Neurotech-Hub/FED4/src/FED4.h

#ifndef FED4_h
#define FED4_h


// note there is a known issue with FastLED 3.10.3 on ESP32-S3 devices
// keep FastLED version 3.10.2 until this issue is fixed in the main FastLED repository
// https://github.com/FastLED/FastLED/issues/5100

#include <Arduino.h>
#include <map>
#include <string>
#include <Adafruit_MCP23X17.h>  // version 2.3.2 
#include "Adafruit_MAX1704X.h"  // version 1.0.3
#include <Stepper.h>  // version 1.1.3
#include <Adafruit_NeoPixel.h> // version 1.15.2
#include <FastLED.h> // version 3.10.2 
#include <Wire.h> 
#include <Adafruit_GFX.h>  // version 1.12.3
#include <Fonts/FreeSans9pt7b.h>
#include <Fonts/Org_01.h>
#include <esp_adc_cal.h>
#include "esp_sleep.h"
#include "RTClib.h" //Adafruit version, 2.1.4
#include <SD.h> //ESP32 version
#include "FS.h"
#include <Adafruit_BME680.h> //version 2.0.5
#include <SPI.h>
#include <driver/adc.h>
#include <ESP_I2S.h>  // New I2S API for ESP32 core 3.x
#include <driver/rtc_io.h>
#include <driver/touch_pad.h>
#include <Preferences.h>
#include <ArduinoJson.h>
#include <Adafruit_LIS3DH.h> //version 1.3.0
#include <Adafruit_Sensor.h>
#include "Adafruit_MLX90393.h" //version 2.0.5
#include "SparkFun_VL53L1X.h" //version 1.2.12
#include "Adafruit_STHS34PF80.h"  //version 1.0.2
#include "Adafruit_VEML7700.h" //version 2.1.6
#include <ESP32Time.h> //version 2.0.6

// Optional Hublink integration - can be excluded via compiler directive
#ifndef FED4_EXCLUDE_HUBLINK
#include <Hublink.h>
#endif

// Pin Definitions
#include "FED4_Pins.h"

// Board Version: set to 162 for v1.6.2 or 163 for v1.6.3
#ifndef FED4_BOARD_VERSION
  #define FED4_BOARD_VERSION 163
#endif

#if FED4_BOARD_VERSION == 163
  #define FED4_BOARD_VERSION_STR "1.6.3"
#elif FED4_BOARD_VERSION == 162
  #define FED4_BOARD_VERSION_STR "1.6.2"
#else
  #error "Unsupported FED4_BOARD_VERSION. Use 162 (v1.6.2) or 163 (v1.6.3)."
#endif

// Device Constants
static const uint8_t LIS3DH_I2C_ADDRESS = 0x19;   // Default I2C address for LIS3DH accelerometer
#if FED4_BOARD_VERSION == 163
  static const uint8_t MLX90393_I2C_ADDRESS = 0x10; // MLX90393 I2C address for board v1.6.3
#else
  static const uint8_t MLX90393_I2C_ADDRESS = 0x0C; // MLX90393 I2C address for board v1.6.2
#endif

// Display Colors and Constants
static const uint8_t DISPLAY_BLACK = 0;
static const uint8_t DISPLAY_WHITE = 1;
static const uint8_t DISPLAY_INVERSE = 2;
static const uint8_t DISPLAY_NORMAL = 3;

// Common display dimensions
static const uint16_t DISPLAY_WIDTH = 144;
static const uint16_t DISPLAY_HEIGHT = 168;

static const uint8_t NUM_STRIP_LEDS = 8;
static const uint8_t NUMPIXELS = 1;
static const uint16_t MOTOR_STEPS = 512;
static const uint8_t MOTOR_SPEED = 24;

static const float TOUCH_THRESHOLD = 0.2; // percentage of baseline change to trigger poke - note that when plugged in by USB this can be much more sensitive than on battery power, due to different grounding
static const char *META_FILE = "/meta.json";

static const char *PREFS_NAMESPACE = "fed4";
static const bool PREFS_RO_MODE = true;
static const bool PREFS_RW_MODE = false;

// current very public-oriented, consider pushing some to private
class FED4 : public Adafruit_GFX
{
public:
    // Constructor declaration only
    FED4();
    static const char libraryVer[];

    // Initialization
    bool begin(const char *programName = nullptr);

    // Hublink integration
    bool useHublink = false; // Default to false, can be set by user
    bool initializeHublink();
    void syncHublink();
    static void onHublinkTimestampReceived(uint32_t timestamp);

    // Motion sensor (STHS34PF80) control
    bool useMotionSensor = true; // Default to true, can be set to false to disable STHS34PF80

    // Button functions
    bool initializeButtons();
    static void IRAM_ATTR onButton1WakeUp();
    static void IRAM_ATTR onButton2WakeUp();
    static void IRAM_ATTR onButton3WakeUp();
    void checkButton1();
    void checkButton2();
    void checkButton3();

    // Corefunctions
    void feed();
    void run();
    
    // Game functions
    void pong();

    // Sleep configuration
    int sleepSeconds = 4; // how many seconds to sleep between timer based wake-ups
    bool sleepyLEDs = true; // Flag to control whether LEDs stay on during sleep (true = LEDs sleep with sleep, false = LEDs stay on during sleep)

    // Menu functions
    void menu();
    void menuStart();
    void menuProgram();
    void menuMouseId();
    void menuSex();
    void menuStrain();
    void menuAge();
    void menuAudio();
    void menuRTC();
    void menuEnd();

    // Sensor polling
    void pollSensors(int minToUpdateSensors = 10);
    void startupPollSensors();

    // Pellet functions
    bool checkForPellet();
    bool didPelletDrop();
    bool pelletPresent;
    bool pelletDropped;
    void initFeeding();
    void handlePelletSettling();
    void handlePelletInWell();
    void finishFeeding();
    void dispense();
    unsigned long pelletDropTime;
    unsigned long pelletWellTime;
    bool dispenseError = false;
    void handleJams();

    // TRRS input/output connector functions
    bool initializeTRRS();
    void outputPulse(uint8_t trss, uint8_t duration);

    // Clock variables
    int currentHour;
    int currentMinute;
    int currentSecond;
    unsigned long unixtime;

    // Stepper motor functionality (defined in FED4_Motor.cpp)
    bool initializeMotor();
    void releaseMotor();
    void minorJamClear();
    void majorJamClear();
    void vibrateJamClear();
    void jammed();

    // Timeout functionality (defined in FED4_Timeout.cpp)
    void timeout(uint16_t min, uint16_t max);

    // Haptic motor vibration stimuli
    void hapticBuzz(uint8_t duration = 100);
    void hapticDoubleBuzz(uint8_t duration = 25);
    void hapticTripleBuzz(uint8_t duration = 5);
    void hapticRumble(uint16_t duration_ms = 300);

    // Touch sensor management (defined in FED4_Touch.cpp)
    bool initializeTouch();
    void calibrateTouchSensors(bool checkStability = false);
    void interpretTouch();
    static void IRAM_ATTR onTouchWakeUp();
    void resetTouchFlags(); // Reset all touch flags to false
    void logTouchEvent(); // Log touch events separately from critical path
    static uint8_t wakePad; // 0=none, 1=left, 2=center, 3=right

    // Pixel an Strip control (defined in FED4_LEDs.cpp)
    // (strip)
    bool initializeStrip();
    void setStripBrightness(uint8_t brightness);
    void colorWipe(const char *colorName, unsigned long wait);
    void colorWipe(uint32_t color, unsigned long wait);
    void stripTheaterChase(const char *colorName, unsigned long wait, unsigned int groupSize = 3, unsigned int numChases = 10);
    void stripTheaterChase(uint32_t color, unsigned long wait, unsigned int groupSize = 3, unsigned int numChases = 10);
    void stripRainbow(unsigned long wait, unsigned int numLoops);
    void randomMotion(float motionStrength, uint32_t color, unsigned long frameDelay = 75, unsigned long durationMs = 3000);
    void randomMotion(float motionStrength, const char *colorName = "blue", unsigned long frameDelay = 75, unsigned long durationMs = 3000);
    void lightsOff();
    void setStripPixel(uint8_t pixel, uint32_t color);
    void leftLight(uint32_t color);
    void leftLight(uint32_t color, uint8_t brightness);
    void centerLight(uint32_t color);
    void centerLight(uint32_t color, uint8_t brightness);
    void rightLight(uint32_t color);
    void rightLight(uint32_t color, uint8_t brightness);
    void setStripPixel(uint8_t pixel, const char *colorName);
    void leftLight(const char *colorName);
    void leftLight(const char *colorName, uint8_t brightness);
    void centerLight(const char *colorName);
    void centerLight(const char *colorName, uint8_t brightness);
    void rightLight(const char *colorName);
    void rightLight(const char *colorName, uint8_t brightness);
    // (pixel)
    bool initializePixel();
    void setPixBrightness(uint8_t brightness);
    void setPixColor(uint8_t r, uint8_t g, uint8_t b, uint8_t brightness = 5);
    void setPixColor(const char *colorName, uint8_t brightness = 5);
    void bluePix(uint8_t brightness = 5);
    void greenPix(uint8_t brightness = 5);
    void redPix(uint8_t brightness = 5);
    void purplePix(uint8_t brightness = 5);
    void yellowPix(uint8_t brightness = 5);
    void cyanPix(uint8_t brightness = 5);
    void whitePix(uint8_t brightness = 5);
    void orangePix(uint8_t brightness = 5);
    void noPix();
    // (shared)
    uint32_t getColorFromString(const char *colorName);

    // Display functions (defined in FED4_Display.cpp)
    bool initializeDisplay();
    void updateDisplay();
    void displayTask();
    void displayMouseId();
    void displayStrain();
    void displaySex();
    void displayAge();
    void displayAudio();
    void displayCounters();
    void displayDateTime();
    void displayEnvironmental();
    void displayBattery();
    void displaySDCardStatus();
    void displayIndicators();
    void startupAnimation();
    void displayInitStatus(const char* message);
    void displayLowBatteryWarning();
    void displayActivityMonitor();
    void displayActivityCounters();

    void serialStatusReport();

    // Sleep management (defined in FED4_Sleep.cpp)
    void sleep(int seconds);
    void sleep();
    void startSleep();
    void wakeUp();
    void handleTouch();
    unsigned long pollSensorsTimer = 0;

    
    bool initializeLDOs();
    void LDO2_ON();
    void LDO2_OFF();
    void LDO3_ON();
    void LDO3_OFF();

    // SD card functions (defined in FED4_SD.cpp)
    bool initializeSD();
    bool createMetaJson();
    bool createLogFile();
    bool logData(const String &newEvent = "");
    String getMetaValue(const char *rootKey, const char *subKey);
    bool setMetaValue(const char *rootKey, const char *subKey, const char *value);
    void setProgram(String program);
    void setMouseId(String mouseId);
    void setSex(String sex);
    void setStrain(String strain);
    void setAge(String age);
    void handleSDCardError();
    bool isSDCardAvailable() const { return sdCardAvailable; }
    
    // Sequence display methods
    void setSequenceDisplay(const String& sequence, int index, int level);

    // Public counters and timing
    int pelletCount;
    int centerCount;
    int leftCount;
    int rightCount;
    int blockPokeCount;
    int blockPelletCount;
    int FR;
    String currentSequence;  // For display purposes
    int currentSequenceIndex; // Current position in sequence
    int currentSequenceLevel; // Current level (FR)
    int wakeCount = 0;
    bool leftTouch;
    bool centerTouch;
    bool rightTouch;
    bool motionDetected = false;  // Track motion detection status
    int motionCount = 0;          // Aggregate motion detections between 5-minute intervals
    float motionPercentage = 0.0; // Percentage of motion detections in the last 5-minute period
    int pollCount = 0;            // Track total number of polls in each 5-minute period
    unsigned long waketime;
    bool lastMotionPositive = false; // Debounce: require two consecutive positives

    // RTC functions
    bool initializeRTC();
    void updateRTC();
    DateTime now();
    void adjustRTC(uint32_t timestamp);
    void updateTime();
    bool forceRTCUpdate = false; // Set to true to force RTC update on next initialization

    // Vitals functions (defined in FED4_Vitals.cpp)
    float getBatteryVoltage();
    float getBatteryPercentage();
    float getTemperature();
    float getHumidity();
    float getPressure();
    float getGasResistance();
    bool getTempAndHumidity(float &temp, float &hum); // Efficient combined read
    bool getAllBME680Data(float &temp, float &hum, float &pres, float &gas); // Get all BME680 values
    float getLux();
    float getWhite();
    bool initializeLightSensor();
    bool reinitializeLightSensor();
    

    // variables to store temp/humidity/pressure/gas and battery info so we don't have to keep pinging the chips every time
    float temperature = -1.0;
    float humidity = -1.0;
    float pressure = -1.0;
    float gasResistance = -1.0;
    float lux = -1.0;
    float white = -1.0;
    float cellVoltage = 0.0;
    float cellPercent = 0.0;
    unsigned long lastPollTime = 0; // make this a large negative so FED polls sensors at first startup

    // Speaker functions (defined in FED4_Speaker.cpp)
    bool initializeSpeaker();
    struct Tone
    {
        uint32_t frequency;
        uint32_t duration_ms;
        float amplitude = 0.25;
    };
    void playTone(uint32_t frequency = 500, uint32_t duration_ms = 200, float amplitude = 0.25);
    void playTones(const Tone *tones, size_t count);
    void enableAmp(bool enable);
    void silence();
    void unsilence();
    void resetSpeaker();

    // Sound stimuli
    void playStartup();
    void bopBeep();
    void resetJingle();
    void menuJingle();
    void lowBeep();
    void highBeep();
    void higherBeep();
    void click();
    void soundSweep(uint32_t startFreq = 500, uint32_t endFreq = 1500, uint32_t duration_ms = 1000);
    void noise(uint32_t duration_ms = 500, float amplitude = 1);

    // "Super Mario"-style sound effects (tone synthesis)
    void marioCoin();
    void marioJump();
    void marioPipe();
    void marioFireball();
    void marioMushroom();

    void setEvent(const String &newEvent)
    {
        event = newEvent;
    }

    String getEvent() const
    {
        return event;
    }

    bool pelletReady;
    bool feedReady;
    int photogate1State;
    String event = "";
    float retrievalTime;
    float pokeDuration = 0.0;
    int touchPadLeftBaseline;
    int touchPadCenterBaseline;
    int touchPadRightBaseline;
    int motorTurns;
    int reBaselineTouches;
    char filename[32];
    bool sdCardAvailable = true; // Track if SD card operations are available
    bool audioSilenced = false; // Track if audio has been silenced

    void clearDisplay();
    void refresh();
    void drawPixel(int16_t x, int16_t y, uint16_t color);



    // Accelerometer functions (defined in FED4_Accel.cpp)
    bool initializeAccel();
    void setAccelRange(lis3dh_range_t range);
    void setAccelPerformanceMode(lis3dh_mode_t mode);
    void setAccelDataRate(lis3dh_dataRate_t dataRate);
    bool getAccelEvent(sensors_event_t *event);
    void readAccel(float &x, float &y, float &z);
    bool accelDataReady();

    // Magnet functions (defined in FED4_Magnet.cpp)
    bool initializeMagnet();
    void setMagnetGain(mlx90393_gain_t gain);
    mlx90393_gain_t getMagnetGain();
    bool readMagnetData(float &x, float &y, float &z);
    bool getMagnetEvent(sensors_event_t *event);
    void configureMagnet(mlx90393_gain_t gain = MLX90393_GAIN_5X);

    // ToF sensor functions (defined in FED4_ToF.cpp)
    bool initializeToF();
    int prox();

    // Motion sensor functions (defined in FED4_Motion.cpp)
    bool initializeMotion();
    bool motion();
    void resetMotionCounters();

    // Drop sensor functions
    bool initializeDropSensor();

    // Memory monitoring function
    void printMemoryStatus();

    ~FED4()
    {
        if (displayBuffer)
        {
            free(displayBuffer);
            displayBuffer = nullptr;
        }
        preferences.end(); // Ensure preferences is closed
    }

private:
    // Hardware objects
    Adafruit_MCP23X17 mcp;
    Adafruit_MAX17048 maxlipo;
    RTC_DS3231 rtc;
    ESP32Time Inrtc;
    Adafruit_BME680 bme;
    Adafruit_NeoPixel pixels;
    Stepper stepper;
    TwoWire I2C_2;
    CRGB strip_leds[NUM_STRIP_LEDS];
    Adafruit_LIS3DH accel;
    Adafruit_MLX90393 magnet;
    Adafruit_STHS34PF80 motionSensor;
    Adafruit_VEML7700 lightSensor;
    I2SClass i2s;  // New I2S driver object for ESP32 core 3.x

// Hublink integration
#ifndef FED4_EXCLUDE_HUBLINK
    Hublink hublink;
#endif
    // Device state variables
    esp_adc_cal_characteristics_t *adc_cal;
    uint32_t millivolts;
    String program;
    String mouseId;
    String sex;
    String strain;
    String age;
    bool dropSensorAvailable; // Flag to store drop sensor availability status
    bool motionSensorInitialized; // Flag to track if motion sensor baseline is established

    // RTC functions
    Preferences preferences;
    String getCompileDateTime();
    bool isNewCompilation();
    void updateCompilationID();

    uint16_t lastTouchValue; // Store the touch value that triggered the interrupt

    uint8_t *displayBuffer = nullptr;
    bool vcom;
    void sendDisplayCommand(uint8_t cmd);

    friend class FED4_Display;
    friend class FED4_LED;
    friend class FED4_Motor;
    friend class FED4_RTC;
    friend class FED4_SD;
    friend class FED4_Touch;
    friend class FED4_Vitals;
    friend class FED4_Feed;
    friend class FED4_Begin;
    friend class FED4_Audio;
    friend class FED4_Magnet;
    friend class FED4_Accel;
    friend class FED4_Menu;
    friend class FED4_Motion;
    friend class FED4_Sleep;
    friend class FED4_Timeout;
    friend class FED4_Prox;
};

// Standard ASCII 5x7 font
static const unsigned char font[] PROGMEM = {
    0x00, 0x00, 0x00, 0x00, 0x00, // space
    0x00, 0x00, 0x5F, 0x00, 0x00, // !
    0x00, 0x07, 0x00, 0x07, 0x00, // "
    // ... rest of font data ...
};

#endif
