Neurotech-Hub/FED4/src/FED4_Feed.cpp

#include "FED4.h"

/**
 * Feeds the mouse by dispensing a pellet from the hopper
 */
void FED4::feed()
{
    initFeeding();
    dispense(); 
    handlePelletSettling();
    handlePelletInWell();
    finishFeeding();
}

void FED4::initFeeding() {
    pelletPresent = checkForPellet();
    pelletDropped = didPelletDrop();
    pelletReady = false;
    dispenseError = false;
    //lightsOff();
    // Serial.println("Feeding!");
}

void FED4::dispense() {
    while (!pelletPresent && !pelletDropped) // while no pellet is present and none has dropped
    {                     
        redPix();
        // check if pellet has dropped or is present
        pelletDropped = didPelletDrop();
        pelletPresent = checkForPellet();
        pelletReady = true;
        
        // Check if button is pressed - if so, fake pelletPresent to exit dispense
        if (digitalRead(BUTTON_1) == 1) {
            hapticDoubleBuzz();
            marioPipe();
            pelletPresent = true;
        }
        
        // Increment block pellet count when pellet drops
        if (pelletDropped) {
            blockPelletCount++;
        }

        // small motor movement
        stepper.step(-10);
        delay(2);
        motorTurns++;
        // delay for 1s roughly each pellet position
        if (motorTurns % 25 == 0)
        {
            Serial.print("Dispensing... ");
            Serial.println(motorTurns/25);
            releaseMotor();
            delay(1000);
        }

        //handle jam movements
        handleJams();
    }
}

void FED4::handleJams() {
        // if stepper is called too many times without a dispense do a small movement to remove jam
        if (motorTurns % 100 == 0)
        {
            minorJamClear();
        }

        if (motorTurns % 200 == 0)
        {
            vibrateJamClear();
        }

        if (motorTurns > 2000)  //how many motorTurns before FED4 stops trying and shuts off?  Each full rotation of the hopper is ~1000 motorTurns
        {
            jammed();
    }
}

void FED4::handlePelletSettling() {
        if (pelletReady) {
        // Serial.println("PelletDrop");
        pelletDropTime = millis();
        pelletCount++;
        logData("PelletDrop");
        }        
  
    releaseMotor();

    // Wait up to 500ms for pellet to settle in well if 500ms passes without detection, set dispenseError to true
    unsigned long startWait = millis();
    bool pelletDetected = false;

    while (millis() - startWait < 500) {
        if (checkForPellet()) {
            pelletDetected = true;
            pelletWellTime = millis();
            break; // Exit if pellet is detected
        }
        delay(10);
    }

    // if pellet is not detected, set dispenseError to true
    if (!pelletDetected) {
        dispenseError = true;
    }

    // Calculate time since pellet drop
    retrievalTime = (millis() - pelletWellTime) / 1000.0;
    // Serial.println("Pellet in Well");
}   

void FED4::handlePelletInWell() {
    pelletPresent = checkForPellet();
    updateDisplay();
    
    // Reset wakePad at start to clear any stale interrupt flags
    wakePad = 0;
    
    while (pelletPresent)
    { // while pellet is in well, monitor for pokes and retrieval time
        bluePix(); 
        pelletPresent = checkForPellet();

        retrievalTime = (static_cast<float>(millis() - pelletWellTime)) / 1000.0f;
        if (retrievalTime > 20)
            break;

        // wakePad mapping (physical pad to touch mapping is rotated):
        // Physical LEFT pad (wakePad=1) → triggers centerTouch
        // Physical CENTER pad (wakePad=2) → triggers rightTouch
        // Physical RIGHT pad (wakePad=3) → triggers leftTouch
        if (wakePad == 3) {  // RIGHT pad interrupt → Left touch
            // Verify touch is actually above threshold (rising edge, not falling edge)
            float rightDev = abs((float)touchRead(TOUCH_PAD_RIGHT) / touchPadRightBaseline - 1.0);
            if (rightDev >= TOUCH_THRESHOLD) {
                unsigned long pokeStartTime = millis();
                leftCount++;
                retrievalTime = 0.0;
                dispenseError = false;
                // Serial.println("LeftWithPellet");
                logData("LeftWithPellet");
                click();
                updateDisplay();
                outputPulse(1, 100);
                // Wait for touch to return to baseline before allowing next detection
                while (abs((float)touchRead(TOUCH_PAD_RIGHT) / touchPadRightBaseline - 1.0) >= TOUCH_THRESHOLD) {
                    delay(10);
                }
                pokeDuration = (float)(millis() - pokeStartTime);
            }
            wakePad = 0; // Reset after handling (whether processed or not)
        }
        else if (wakePad == 2) {  // CENTER pad interrupt → Right touch
            // Verify touch is actually above threshold (rising edge, not falling edge)
            float centerDev = abs((float)touchRead(TOUCH_PAD_CENTER) / touchPadCenterBaseline - 1.0);
            if (centerDev >= TOUCH_THRESHOLD) {
                unsigned long pokeStartTime = millis();
                rightCount++;
                retrievalTime = 0.0;
                dispenseError = false;
                // Serial.println("CenterWithPellet");
                logData("CenterWithPellet"); 
                click();
                updateDisplay();
                bluePix();
                outputPulse(2, 100);
                // Wait for touch to return to baseline before allowing next detection
                while (abs((float)touchRead(TOUCH_PAD_CENTER) / touchPadCenterBaseline - 1.0) >= TOUCH_THRESHOLD) {
                    delay(10);
                }
                pokeDuration = (float)(millis() - pokeStartTime);
            }
            wakePad = 0; // Reset after handling (whether processed or not)
        }
        else if (wakePad == 1) {  // LEFT pad interrupt → Center touch
            // Verify touch is actually above threshold (rising edge, not falling edge)
            float leftDev = abs((float)touchRead(TOUCH_PAD_LEFT) / touchPadLeftBaseline - 1.0);
            if (leftDev >= TOUCH_THRESHOLD) {
                unsigned long pokeStartTime = millis();
                centerCount++;
                retrievalTime = 0.0;
                dispenseError = false;
                // Serial.println("CenterWithPellet");
                logData("CenterWithPellet");
                click();
                updateDisplay();
                bluePix();
                outputPulse(2, 100);
                // Wait for touch to return to baseline before allowing next detection
                while (abs((float)touchRead(TOUCH_PAD_LEFT) / touchPadLeftBaseline - 1.0) >= TOUCH_THRESHOLD) {
                    delay(10);
                }
                pokeDuration = (float)(millis() - pokeStartTime);
            }
            wakePad = 0; // Reset after handling (whether processed or not)
        }
        
        delay(10); // Small delay to prevent excessive CPU usage
    }
}

void FED4::finishFeeding() {
        purplePix();
    // Serial.println("Pellet Removed");

    if (pelletReady) {
        if (dispenseError) {
            retrievalTime = 0.0;
            logData("PelletNotDetected");
        } else {
            logData("PelletTaken");
            blockPokeCount = 0;  // Reset block poke count when pellet is taken
        }
    }

    // Reset variables
    pelletReady = false;
    retrievalTime = 0.0;
    dispenseError = false;
    
    // Reset touch states after handling the feed
    leftTouch = false;
    centerTouch = false;
    rightTouch = false;

    // Rebaseline touch sensors
    reBaselineTouches = 3;
    if ((leftCount + rightCount + centerCount) % reBaselineTouches == 0 && (leftCount + rightCount + centerCount) > 5)
    {
        calibrateTouchSensors();
    }

}

/** 
 * Checks if the pellet is present in the center port
 * 
 * @return bool - true if pellet is present, false otherwise
 */
bool FED4::checkForPellet()
{
    return !mcp.digitalRead(EXP_PHOTOGATE_1);
}

/** 
 * Checks if the pellet is present dropped 
 * 
 * @return bool - true if pellet dropped, false otherwise
 */
bool FED4::didPelletDrop()
{
    if (dropSensorAvailable) {
        //With drop sensor use:
        return !mcp.digitalRead(EXP_PHOTOGATE_4);
    } else {
        //Without drop sensor use:
        return false; // Always return false when sensor is not available
    }
}

/**
 * Initializes the drop sensor and checks its status
 * 
 * @return bool - true if drop sensor is working (HIGH), false if broken or not present (LOW)
 */
bool FED4::initializeDropSensor()
{
    // Read the drop sensor status
    bool sensorStatus = mcp.digitalRead(EXP_PHOTOGATE_4);
    
    // Set the flag based on sensor status
    dropSensorAvailable = sensorStatus;
    
    // Return true if HIGH (sensor is good), false if LOW (broken or not present)
    return sensorStatus;
}
