Neurotech-Hub/FED4/src/FED4_Buttons.cpp

#include "FED4.h"

// Interrupt handler for BUTTON_1
void IRAM_ATTR FED4::onButton1WakeUp() {
}

// Interrupt handler for BUTTON_2
void IRAM_ATTR FED4::onButton2WakeUp() {
}

// Interrupt handler for BUTTON_3
void IRAM_ATTR FED4::onButton3WakeUp() {
}

bool FED4::initializeButtons() {
    // Configure BUTTON_1, BUTTON_2, and BUTTON_3 as inputs with internal pulldown
    gpio_config_t io_conf = {};
    io_conf.intr_type = GPIO_INTR_HIGH_LEVEL;
    io_conf.pin_bit_mask = (1ULL << BUTTON_1) | (1ULL << BUTTON_2) | (1ULL << BUTTON_3);
    io_conf.mode = GPIO_MODE_INPUT;
    io_conf.pull_down_en = GPIO_PULLDOWN_ENABLE;
    io_conf.pull_up_en = GPIO_PULLUP_DISABLE;
    
    esp_err_t err = gpio_config(&io_conf);
    if (err != ESP_OK) {
        Serial.println("Failed to configure GPIO");
        return false;
    }
    
    // Enable wake-up on GPIO for all buttons
    err = gpio_wakeup_enable((gpio_num_t)BUTTON_1, GPIO_INTR_HIGH_LEVEL);
    if (err != ESP_OK) {
        Serial.println("Failed to enable GPIO wakeup for Button 1");
        return false;
    }
    
    err = gpio_wakeup_enable((gpio_num_t)BUTTON_2, GPIO_INTR_HIGH_LEVEL);
    if (err != ESP_OK) {
        Serial.println("Failed to enable GPIO wakeup for Button 2");
        return false;
    }
    
    err = gpio_wakeup_enable((gpio_num_t)BUTTON_3, GPIO_INTR_HIGH_LEVEL);
    if (err != ESP_OK) {
        Serial.println("Failed to enable GPIO wakeup for Button 3");
        return false;
    }
    
    err = esp_sleep_enable_gpio_wakeup();
    if (err != ESP_OK) {
        Serial.println("Failed to enable GPIO wakeup in sleep");
        return false;
    }
    return true;
}

// Checks if feed button is held and dispenses test pellet after 1 second
void FED4::checkButton1() {
  int holdTime = 0;
  while (digitalRead(BUTTON_1) == 1) {
    delay(100);
    holdTime += 100;
    if (holdTime >= 1000) {
        marioMushroom();
        delay (500);
        Serial.println("********** TEST PELLET DISPENSE **********");
        feed();
        break;
    }
  }
}

// Checks if reset button is held and performs device reset after 1 second
void FED4::checkButton2() {
  int holdTime = 0;
  while (digitalRead(BUTTON_2) == 1) {
    delay(100);
    holdTime += 100;
    if (holdTime >= 1000) {
        colorWipe("red", 100); // red
        resetJingle();
        Serial.println("********** BUTTON 2 FORCED RESET! **********");
        esp_restart();
        break;
    }
  }
}

// Checks if Button 3 is held for silence toggle (500ms) or menu (1500ms)
void FED4::checkButton3() {
  int holdTime = 0;
  
  while (digitalRead(BUTTON_3) == 1) {
    delay(100);
    holdTime += 100;
    
    // At 500ms: Provide haptic feedback for audio toggle threshold
    if (holdTime == 500) {
      // temporarily unmute audio even if it is silenced
      digitalWrite(AUDIO_SD, HIGH);
      click();
    }
    
    // At 1500ms: Enter menu with double haptic feedback (no audio toggle)
    if (holdTime >= 1500) {
        hapticDoubleBuzz(100);
        Serial.println("********** BUTTON 3 MENU START **********");
        menu();
        break;
    }
  }
  
  // Only toggle audio if button was released between 500ms and 1500ms
  if (holdTime >= 500 && holdTime < 1500) {
    if (audioSilenced) {
        unsilence();
        Serial.println("********** AUDIO ENABLED **********");
    } else {
        silence();
        Serial.println("********** AUDIO DISABLED **********");
    }
  }
}
