Neurotech-Hub/FED4/src/FED4_Serial.cpp

#include "FED4.h"

void FED4::serialStatusReport()
{
    if (wakeCount == 0) {
        Serial.println("********** Ready to go! **********");
    }
    
    // Check if motion sensor is disabled
    if (!useMotionSensor || isnan(motionPercentage)) {
        Serial.printf("%02d/%02d/%02d %02d:%02d:%02d | %.1fC - %.1f%% - %.1fhPa - %.1fKΩ | %.1fLux | %.2fV(%.1f%%) | No Motion | Pel %d | Left/Cent/Right %d/%d/%d | Poke %.0fms | Mem %d | Wake %d\n",        
            rtc.now().month(), rtc.now().day(), rtc.now().year(), rtc.now().hour(), rtc.now().minute(), rtc.now().second(),
            temperature, humidity, pressure, gasResistance, lux, 
            cellVoltage, cellPercent,
            pelletCount,    
            leftCount, centerCount, rightCount,
            pokeDuration,
            ESP.getFreeHeap(),
            wakeCount);
    } else {
        Serial.printf("%02d/%02d/%02d %02d:%02d:%02d | %.1fC - %.1f%% - %.1fhPa - %.1fKΩ | %.1fLux | %.2fV(%.1f%%) | Motion %d(%.1f%%) | Pel %d | Left/Cent/Right %d/%d/%d | Poke %.0fms | Mem %d | Wake %d\n",        
            rtc.now().month(), rtc.now().day(), rtc.now().year(), rtc.now().hour(), rtc.now().minute(), rtc.now().second(),
            temperature, humidity, pressure, gasResistance, lux, 
            cellVoltage, cellPercent,
            motionDetected, motionPercentage,
            pelletCount,    
            leftCount, centerCount, rightCount,
            pokeDuration,
            ESP.getFreeHeap(),
            wakeCount);
    }
}
